jeevan8232/macrokeyboard/3d files/stl/Encoder knob horizontal scroll.stl

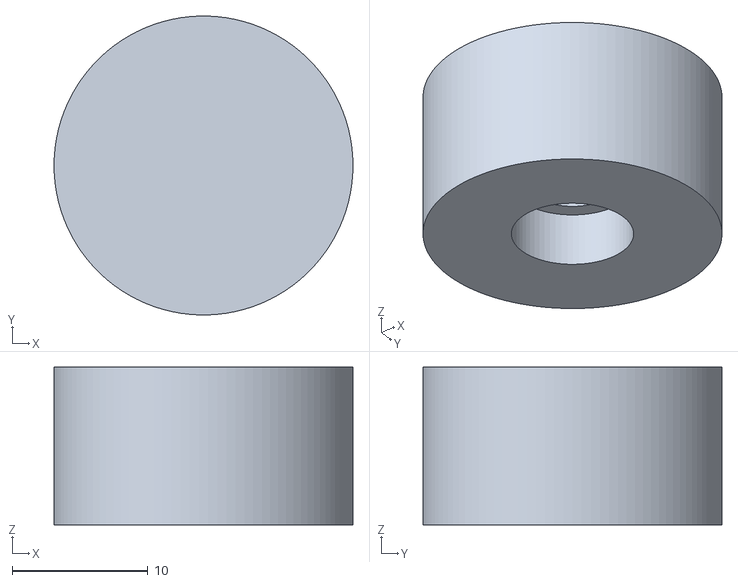
[picture p12: CAD file, 2026-02-27]
3d files/stl/Encoder knob horizontal scroll.stl
22.0 x 22.0 x 11.6
