jeevan8232/macrokeyboard/3d files/stl/Ledstrip cover.stl

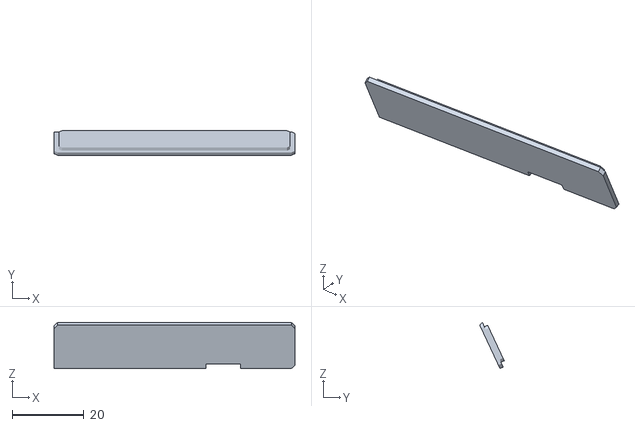
[picture p13: CAD file, 2026-02-27]
3d files/stl/Ledstrip cover.stl
67.0 x 6.83 x 12.8
